jpaulovf/IE309X/EnergyMeter_Pio/EnergyMeter/src/run.h

/*************************************
 * run.h - Função principal
 * -----------------------------------
 * 
 * autor: jpaulovf@gmail.com
 * 
 *************************************/

// Modo debug
// Escreva 1 para entrar no modo de Debug
// Neste modo, valores fakes serão enviados para o Blynk
#define DEBUGMODE 0

// Constante W.h/LSB (obtida através da calibração)
#define WHLSB 0.000172F

// Pino de interrupção do ADE
#define ADE_IRQ_PIN 26

// Intervalo de medição do Blynk em segundos
#define BLYNK_MEAS_TIMER 10000L

// Timeout em segundos
#define TOUT_S 10


// Protótipo da função run
void run();
