jpaulovf/IE309X/EnergyMeter_Pio/EnergyMeter/src/Tests.cpp

/*************************************
 * Tests.cpp - Testes unitários
 * -----------------------------------
 * 
 * autor: jpaulovf@gmail.com
 * 
 *************************************/

#include "Tests.h"
#include <Arduino.h>
#include <DataStorage.h>
#include <ADE7758.h>
#include <stdint.h>
#include <RGBLed.h>

//#include <BlynkSimpleEsp32.h>
#include <WiFi.h>
#include <WiFiClient.h>

#include <cstdlib>
#include <ctime>

/* ------------------------------------- *
 * Globais                               *
 * ------------------------------------- */
volatile uint8_t irqflag = 0;



/* ------------------------------------- *
 * Funções                               *
 * ------------------------------------- */

/*
 * Testa o LED RGB
 */
void testRGBLed(){

  RGBLed *myled = new RGBLed(PIN_LED_R, PIN_LED_G, PIN_LED_B);
  myled->write(0, 0, 0);  // Off

  while (1){

    myled->write(1, 0, 0);  // Red
    delay(500);
    myled->write(0, 1, 0);  // Green
    delay(500);
    myled->write(0, 0, 1);  // Blue
    delay(500);

  }


}

/*
 * Testa o armazenamento na EEPROM
 */
void testStorage(){

  char msg[14] = "Jall Sondwich";
  char buf[14];

  // Clearing buffer
  for (int i=0; i<14; i++){
    buf[i] = 0;
  }

  Serial.begin(9600);

  Serial.println("EEPROM Storage Test!");
  Serial.println("Reading 14 bytes from EEPROM address 0...");

  getStoredData(0, &buf[0], 14);

  Serial.print(" Data = ");
  Serial.println(buf);

  Serial.println("Writing 14 bytes to EEPROM address 0...");

  storeData(0, &msg[0], 14);

  Serial.println("Reading 14 bytes from EEPROM address 0...");

  getStoredData(0, &buf[0], 14);
  Serial.print(" Data = ");
  Serial.println(buf);
  
}

/*
 * Testa a comunicação com o AD7758
 */
void testADE7758(){

  ADE7758Device *ade = new ADE7758Device();
  uint8_t addr;
  uint8_t size;
  uint8_t operation = 0;
  uint8_t data[10];
  char inputBuffer[3];
  char key;
  uint32_t finalData;

  // Inicializando a serial
  Serial.begin(9600);
  Serial.setTimeout(60000);


  // Limpando os buffers
  for (int i=0; i<10; i++){
    data[i] = 0;
  }
  for (int i=0; i<3; i++){
    inputBuffer[i] = 0;
  }
  
  // Loop para pegar dados do usuário
  while (1){

    Serial.println("*** ENTER REGISTER PARAMETERS ***");

    // Escolhendo a operação (R/W)
    Serial.println("\nSelect operation: (W)rite, (R)ead");
    Serial.readBytes(&key, 1);
    if (key == 'w' || key == 'W'){
      operation = 1;
    }
    else{
      operation = 0;
    }
    Serial.print("You entered ");
    if (operation == 1){
      Serial.println("WRITE");
    }
    else{
      Serial.println("READ");
    }

    // Lendo o endereço do registrador
    Serial.println("\nRegister address (hexa): ");
    Serial.readBytesUntil('\n', (char *) inputBuffer, 2);
    while (Serial.available()){
      Serial.read();
    }
    inputBuffer[2] = 0;
    addr = (uint8_t) strtol(inputBuffer, 0, 16);
    Serial.print("You entered address 0x");
    Serial.println(addr, HEX);

    // Lendo o numero de bytes
    for (int i=0; i<3; i++){
      inputBuffer[i] = 0;
    }
    Serial.println("\nNumber of data bytes: ");
    Serial.readBytesUntil('\n', (char *) inputBuffer, 2);
    while (Serial.available()){
      Serial.read();
    }
    inputBuffer[2] = 0;
    size = (uint8_t) strtol(inputBuffer, 0, 10);
    if (size > 10){
      size = 10;
    }
    Serial.print("You entered ");
    Serial.println(size);

    // Lendo os dados, caso escrita
    if (operation == 1){
      for (int i=0; i<10; i++){
        data[i] = 0;
      }
      for (int i=0; i<3; i++){
        inputBuffer[i] = 0;
      }
      for (int i=0; i<size; i++){
        Serial.print("\nData[");
        Serial.print(i);
        Serial.println("] (hexa): ");
        Serial.readBytesUntil('\n', (char *) inputBuffer, 2);
        while (Serial.available()){
          Serial.read();
        }
        inputBuffer[2] = 0;
        data[i] = (uint8_t) strtol(inputBuffer, 0, 16);
        Serial.print("You entered 0x");
        Serial.println(data[i], HEX);
      }
    }

    // Iniciando operação
    if (operation == 1){
      Serial.println("---------------------------");
      Serial.print("Writing ");
      Serial.print(size);
      Serial.print(" bytes on register 0x");
      Serial.println(addr, HEX);
      ade->writeRegister(addr, size, data);
      Serial.println("DONE\n");
    }
    else{
      Serial.println("---------------------------");
      Serial.print("Reading ");
      Serial.print(size);
      Serial.print(" bytes from register 0x");
      Serial.println(addr, HEX);
      ade->readRegister(addr, size, data);
      finalData = 0;
      for (int i=0; i<size; i++){
        finalData |= data[i]<<(8*(size-1-i));
      }
      Serial.print("Read value is: ");
      Serial.print(finalData);
      Serial.print(" (0x");
      Serial.print(finalData, HEX);
      Serial.println(")\n");
    }

  }
  
}

/*
 *  Interrupção de Zero-Crossing
 */ 
void IRAM_ATTR IRQHandler(){

  digitalWrite(DEBUG_LED, !digitalRead(DEBUG_LED));
  irqflag = 1;

}

/*
 * Testa a medição de VRMS com interrupção de ZX
 */
void testVRMS(){

  ADE7758Device *ade = new ADE7758Device();
  const byte interruptPin = 39; //14
  uint8_t data[2];
  uint8_t vrms_data[3];
  uint32_t vrms;
  uint32_t meas_counter = 0;
  uint64_t vrms_mean = 0;

  Serial.begin(9600);
  pinMode(39, INPUT);
  pinMode(DEBUG_LED, OUTPUT);
  digitalWrite(DEBUG_LED, HIGH);

  // Configurando os registradores
  Serial.println("Configuring registers...");

  // Registrador MODE
  data[0] = 0x60;
  ade->writeRegister(0x09, 2, data);

  // Registrador INTERRUPT ENABLE
  data[0] = 0x00;
  data[1] = 0x10;
  ade->writeRegister(0x0A, 2, data);

  // Registrador de correção de offset VRMS
  data[0] = 0x00;
  data[1] = 0x00;
  ade->writeRegister(0x19, 2, data);

  // Lendo os registradores pra ver se tá certo
  ade->readRegister(0x09, 2, data);
  Serial.print("MODE = 0x");
  Serial.print(data[0], HEX);
  Serial.println(data[1], HEX);

  ade->readRegister(0x0B, 2, data);
  Serial.print("Interrupt Status = 0x");
  Serial.print(data[0], HEX);
  Serial.println(data[1], HEX);

  // Resetando flags
  ade->readRegister(0x0C, 2, data);

  attachInterrupt(digitalPinToInterrupt(interruptPin), IRQHandler, FALLING);

  while (1){

    if (irqflag == 1){

      //Serial.println("Interrupt detected. Reading VRMS...");

      ade->readRegister(0x17, 3, vrms_data);
      vrms = ((uint32_t) vrms_data[0]) << 16 |
             ((uint32_t) vrms_data[1]) << 8 |
             ((uint32_t) vrms_data[2]);

      /*
      Serial.print("VRMS = ");
      Serial.print(vrms);
      Serial.print(" (0x");
      Serial.print(vrms, HEX);
      Serial.println(")");
      */

      meas_counter++;
      vrms_mean += vrms;

      if (meas_counter == 256){
        meas_counter = 0;
        vrms = (uint32_t) (vrms_mean >> 8);
        vrms_mean = 0;
        Serial.print("VRMS = ");
        Serial.print(vrms);
        Serial.print(" (0x");
        Serial.print(vrms, HEX);
        Serial.println(")");
      }

      // Resetando o registrador de flags 
      ade->readRegister(0x0C, 2, data); 

    }

  }

}


/*
 *  Calibra a constante de W.h
 */

void IRAM_ATTR IRQHandler2(){

  digitalWrite(DEBUG_LED, !digitalRead(DEBUG_LED));
  irqflag = 1;

}
  
void whCal(){

  ADE7758Device *ade = new ADE7758Device();
  //const byte interruptPin = 39;
  uint8_t data8;
  uint16_t data16;
  uint32_t data24;
  uint16_t awh, bwh, cwh;
  float f_awh, f_bwh, f_cwh;
  float testwh = 0;

  //const float whlsb = 0.000521;
  //const float whlsb = 0.000058;
  const float whlsb = 0.000172;

  Serial.begin(9600);
  pinMode(26, INPUT);
  pinMode(DEBUG_LED, OUTPUT);
  digitalWrite(DEBUG_LED, LOW);
  Serial.println("CALIBRATION!");

  // Atribuindo a interrupção
  attachInterrupt(digitalPinToInterrupt(26), IRQHandler2, FALLING);

  // Teste
  data16 = ade->read16(0x48);
  Serial.print("VARCFDEN = 0x");
  Serial.println(data16, HEX);


    // Configurando WAVFORM
  //data8 = 0x04;
  //ade->write8(REG_WAVEFORM, data8);
  //data8 = ade->read8(REG_WAVEFORM);
  //Serial.print("WAVEFORM = 0x");
  //Serial.println(data8, HEX);

  // Escrevendo ACPFNUM (16) e ACPFDEN (16)
  data16 = 0x0000;
 
  ade->write16(REG_APCFDEN, data16);
  data16 = ade->read16(REG_APCFDEN);
  Serial.print("APCFDEN = 0x");
  Serial.println(data16, HEX);

  ade->write16(REG_APCFNUM, data16);
  data16 = ade->read16(REG_APCFNUM);
  Serial.print("APCFNUM = 0x");
  Serial.println(data16, HEX);

  // Limpando os xWG (16)
  data16 = 0x0000;
  
  ade->write16(REG_AWG, data16);
  data16 = ade->read16(REG_AWG);
  Serial.print("AWG = 0x");
  Serial.println(data16, HEX);

  ade->write16(REG_BWG, data16);
  data16 = ade->read16(REG_BWG);
  Serial.print("BWG = 0x");
  Serial.println(data16, HEX);

  ade->write16(REG_CWG, data16);
  data16 = ade->read16(REG_CWG);
  Serial.print("CWG = 0x");
  Serial.println(data16, HEX);

  // Selecionar a fase no MMODE (8)

  data8 = 0xFC; // Fase A
  //data8 = 0x01; // Fase B
  //data8 = 0x02; // Fase C
  ade->write8(REG_MMODE, data8);
  data8 = ade->read8(REG_MMODE);
  Serial.print("MMODE = 0x");
  Serial.println(data8, HEX);

  // Configurar o LCYCMODE (8)
  data8 = 0x09;
  ade->write8(REG_LCYCMODE, data8);
  data8 = ade->read8(REG_LCYCMODE);
  Serial.print("LCYCMODE = 0x");
  Serial.println(data8, HEX);

  // Configurar o LINECYC (16) para 60 ciclos
  data16 = 0x01F4;
  ade->write16(REG_LINECYC, data16);
  data16 = ade->read16(REG_LINECYC);
  Serial.print("LINECYC = 0x");
  Serial.println(data16, HEX);

  // Configurar a máscara de interrupções (24) para pegar LENERGY
  data24 = 0x001000;
  ade->write24(REG_MASK, data24);
  data24 = ade->read24(REG_MASK);
  Serial.print("MASK = 0x");
  Serial.println(data24, HEX);

  while(1){

    //irqflag = 0;

    // Resetando o status de interrupção (ler RSTATUS (24))
    //delay(100);
    ade->read24(REG_RSTATUS);
    

    // Esperando a interrupção
    while (irqflag == 0);
    irqflag = 0;
    //delay(2000);

    // Lendo o registrador de watt.h (16) da fase
    awh = ade->read16(REG_AWATTHR);  // Fase A
    bwh = ade->read16(REG_BWATTHR);  // Fase B
    cwh = ade->read16(REG_CWATTHR);  // Fase C

    f_awh = ((float) awh)*whlsb;
    f_bwh = ((float) bwh)*whlsb;
    f_cwh = ((float) cwh)*whlsb;

    testwh += f_awh;

    // Printando
    Serial.println("-------------------");

    Serial.print("AWATTHR = 0x");
    Serial.print(awh, HEX);
    Serial.print(" (");
    Serial.print(f_awh);
    Serial.println(" Wh)");

    Serial.print("BWATTHR = 0x");
    Serial.print(bwh, HEX);
    Serial.print(" (");
    Serial.print(f_bwh);
    Serial.println(" Wh)");

    Serial.print("CWATTHR = 0x");
    Serial.print(cwh, HEX);
    Serial.print(" (");
    Serial.print(f_cwh);
    Serial.println(" Wh)");

    Serial.print("Accumulated = ");
    Serial.print(testwh);
    Serial.println(" Wh");

    Serial.println("-------------------");

    //delay(500);

  }

}

// Testa se a placa está viva
void checkIfAlive(){

  pinMode(DEBUG_LED, OUTPUT);
  Serial.begin(9600);

  while(1){

    digitalWrite(DEBUG_LED, !digitalRead(DEBUG_LED));

    Serial.println("I AM ALIVE!");

    delay(500);

  }

}

// Testa o Blynk
//
//void timerEvent(){
//
//  uint16_t number;
//
//  srand(time(NULL));
//
//  number = rand() % 10 + 1;
//
//  Blynk.virtualWrite(V0, number);
//
//}

//void testBlynk(){
//
//  char auth[] = "a4079471987f4abd9c2a25ad8543e485";
//  char ssid[] = "AndroidAPDBD3";
//  char pass[] = "rdow3020";
//
//  BlynkTimer timer;
//
//  Serial.begin(9600);
//
//  Blynk.begin(auth, ssid, pass);
//
//  timer.setInterval(1000, timerEvent);
//
//  while(1){
//
//    Blynk.run();
//    timer.run();
//
//  }
//
//
//}
